r223908/pj3_ea801_r223908_a213293/docs/2_images/cvt_cad-2_pj3_v0.png

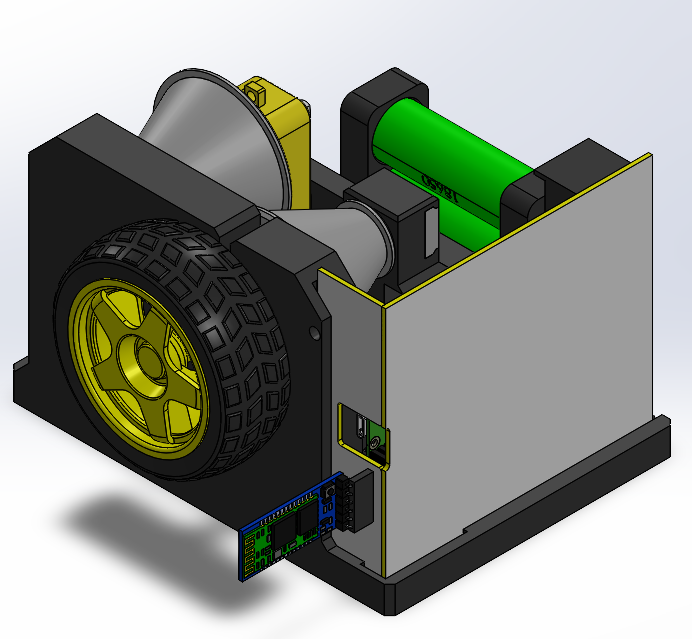
docs/2_images/cvt_cad-2_pj3_v0.png
