r223908/pj3_ea801_r223908_a213293/docs/2_images/1_montagem/eletrica_1.jpg

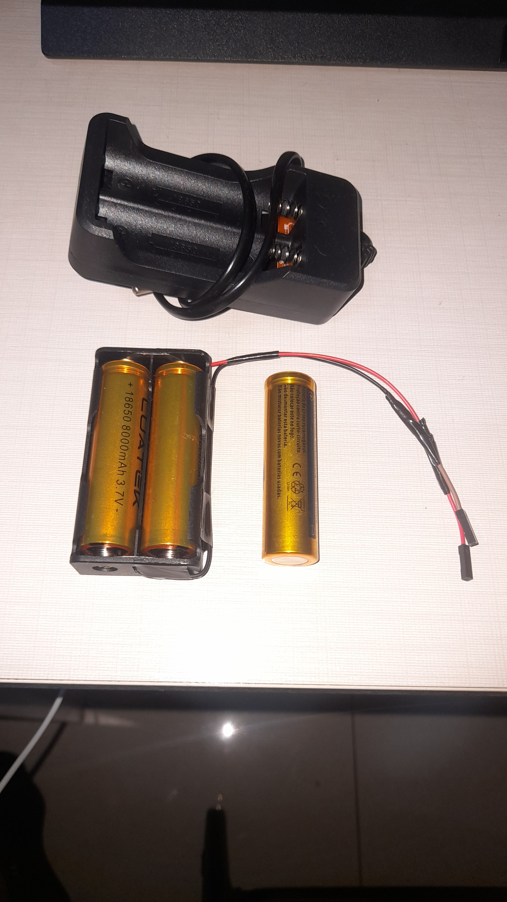
docs/2_images/1_montagem/eletrica_1.jpg
